Oliv4945/STM32L052_Breadboard/STM32L052_BB_Tests.ioc

Mcu.UserName=STM32L052K8Tx
PA8.GPIO_Label=MOSFET
PA8.Signal=GPIO_Output
PA9.GPIO_Label=WS2812
PA9.Signal=GPIO_Output
PB6.Signal=USART1_TX
PB7.Signal=USART1_RX
PC14-OSC32_IN.Signal=RCC_OSC32_IN
PC15-OSC32_OUT.Signal=RCC_OSC32_OUT
